lucasrguerra/power_vision/boards/v3.0/schematic.pdf

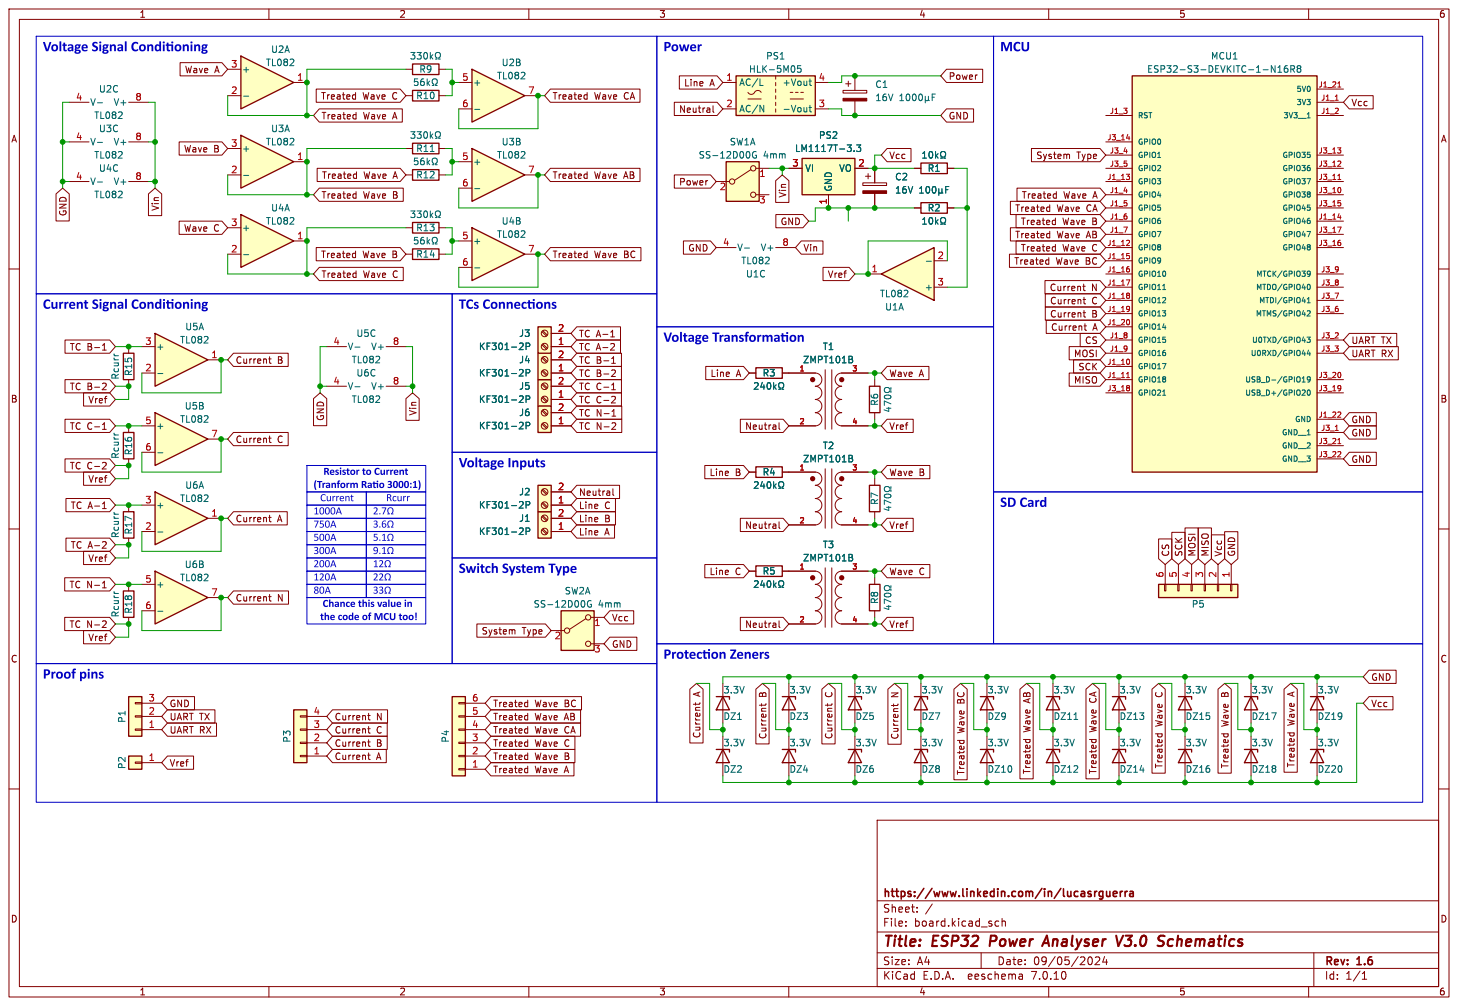
[picture p25: page 1]

MCU
Neutral Vin Neutral Power Line A GND

System Type Treated Wave A

Treated Wave B
Treated Wave AB Current C
Treated Wave C
Treated Wave BC

Line B UART TX GND

Id: 1/1 Title: ESP32 Power Analyser V3.0 Schematics
